kins-dev/igrill-smoker/scripts/pygrill/tests/test_leds.py

#!/usr/bin/env python3
"""
  Copyright (c) 2019:   Scott Atkins <scott@kins.dev>
                        (https://git.kins.dev/igrill-smoker)
  License:              MIT License
                        See the LICENSE file
"""

__author__ = "Scott Atkins"
__version__ = "1.4.0"
__license__ = "MIT"

import unittest
import unittest.mock as mock
from ..board import leds
from ..common.constant import SSRC, CONFIG


class Test_LEDs(unittest.TestCase):

    def test_Leds(self):
        with mock.patch('pygrill.board.leds.pigpio.pi') as mockitem:
            mock_pigpio_inst = mockitem.return_value
            for fun in SSRC.BOARD.ITEMS["LED"]:
                for board in SSRC.BOARD.ITEMS["LED"][fun]:
                    leds.SetLED(board, fun, False)
                    if(SSRC.BOARD.VALUES_STANDARD == SSRC.BOARD.ITEMS["LED"][fun][board][SSRC.BOARD.ITEM_VALUE]):
                        mock_pigpio_inst.write.assert_called_once_with(
                            SSRC.BOARD.ITEMS["LED"][fun][board][SSRC.BOARD.ITEM_IO], 0)
                    elif(SSRC.BOARD.VALUES_INVERTED == SSRC.BOARD.ITEMS["LED"][fun][board][SSRC.BOARD.ITEM_VALUE]):
                        mock_pigpio_inst.write.assert_called_once_with(
                            SSRC.BOARD.ITEMS["LED"][fun][board][SSRC.BOARD.ITEM_IO], 1)
                    else:
                        mock_pigpio_inst.write.assert_not_called()
                    mock_pigpio_inst.reset_mock()
                    leds.SetLED(board, fun, True)
                    if(SSRC.BOARD.VALUES_STANDARD == SSRC.BOARD.ITEMS["LED"][fun][board][SSRC.BOARD.ITEM_VALUE]):
                        mock_pigpio_inst.write.assert_called_once_with(
                            SSRC.BOARD.ITEMS["LED"][fun][board][SSRC.BOARD.ITEM_IO], 1)
                    elif(SSRC.BOARD.VALUES_INVERTED == SSRC.BOARD.ITEMS["LED"][fun][board][SSRC.BOARD.ITEM_VALUE]):
                        mock_pigpio_inst.write.assert_called_once_with(
                            SSRC.BOARD.ITEMS["LED"][fun][board][SSRC.BOARD.ITEM_IO], 0)
                    else:
                        mock_pigpio_inst.write.assert_not_called()
                    mock_pigpio_inst.reset_mock()


if __name__ == '__main__':
    print("BASEPATH=" + CONFIG.BASEPATH)
    print("MAX: {}".format(SSRC.PWM.LIMIT_MAX))
    print("MIN: {}".format(SSRC.PWM.LIMIT_MIN))
    unittest.main()
